Rafael-Ramildes-Ferreira/CPR-Baby-Dummy-Instrumentation/include/main.h

#ifndef _MAIN_H
#define _MAIN_H

#include "buildconfig.h"

#define MY_DEBUG_PRINT(...) do{ printf(__VA_ARGS__ ); } while( false )

void print_mem(void * obj, size_t size);

/* Exported functions */
void error_handler();

#endif
