Rafael-Ramildes-Ferreira/CPR-Baby-Dummy-Instrumentation/include/chest_compressions.h

#ifndef _CHEST_COMPRESSION_H
#define _CHEST_COMPRESSION_H

#include <Adafruit_VL6180X.h>
#include "buildconfig.h"

#ifdef FREQUENCY_ON_ESP
// Peak and valley finder algorithm configuration
#define BUFFER_SIZE	(3)
#endif


class ChestCompression{
	public:
		int begin();
		double calc_distance();
		double get_distance();
	#ifdef FREQUENCY_ON_ESP
		double calc_frequency();
		double get_frequency();
	#endif

	private:
	#ifdef FREQUENCY_ON_ESP
		double last_peak();
		double last_valley();
		double update_frequency();

		double readings[BUFFER_SIZE];
		unsigned int buffer_index;

		double mean,deviation;
		unsigned int new_valley_time, old_valley_time;
		unsigned int last_peak_time;
		bool frequency_isOld;
		double frequency;
		long int frequency_update_time;
	#endif

		Adafruit_VL6180X dist_sensor;
		double distance;
};

#endif
